Christian-OSU/ECEN4013Projec2/Testing/GPS/GPSParse/GPSParse.ino

#include <Adafruit_GPS.h>

#define GPSSerial Serial1
Adafruit_GPS GPS(&GPSSerial);

void setup() {
  Serial.begin(115200);
  while (!Serial) delay(10);

  GPS.begin(9600);
  GPS.sendCommand(PMTK_SET_NMEA_OUTPUT_RMCGGA);  // Essential sentences
  GPS.sendCommand(PMTK_SET_NMEA_UPDATE_1HZ);     // 1 Hz update rate
  Serial.println("Adafruit GPS started...");
}

void loop() {
  // Read incoming data from GPS
  //char c = GPS.read();

  // Uncomment if you want to see raw NMEA data:
  // if (c) Serial.write(c);

  // Parse new NMEA sentence when available
  Serial.print("\nTime: ");
    Serial.print(GPS.hour, DEC); Serial.print(':');
    Serial.print(GPS.minute, DEC); Serial.print(':');
    Serial.print(GPS.seconds, DEC); Serial.print('.');
    Serial.println(GPS.milliseconds);
    Serial.print("Date: ");
    Serial.print(GPS.day, DEC); Serial.print('/');
    Serial.print(GPS.month, DEC); Serial.print("/20");
    Serial.println(GPS.year, DEC);
    Serial.print("Fix: "); Serial.print((int)GPS.fix);
    Serial.print(" quality: "); Serial.println((int)GPS.fixquality); 
    if (GPS.fix) {
      Serial.print("Location: ");
      Serial.print(GPS.latitude, 4); Serial.print(GPS.lat);
      Serial.print(", "); 
      Serial.print(GPS.longitude, 4); Serial.println(GPS.lon);
      Serial.print("Location (in degrees, works with Google Maps): ");
      Serial.print(GPS.latitudeDegrees, 4);
      Serial.print(", "); 
      Serial.println(GPS.longitudeDegrees, 4);
      
      Serial.print("Speed (knots): "); Serial.println(GPS.speed);
      Serial.print("Angle: "); Serial.println(GPS.angle);
      Serial.print("Altitude: "); Serial.println(GPS.altitude);
      Serial.print("Satellites: "); Serial.println((int)GPS.satellites);
  }
}
